erdometo/fluxgate-project/Pictures/1686348193057.jpg

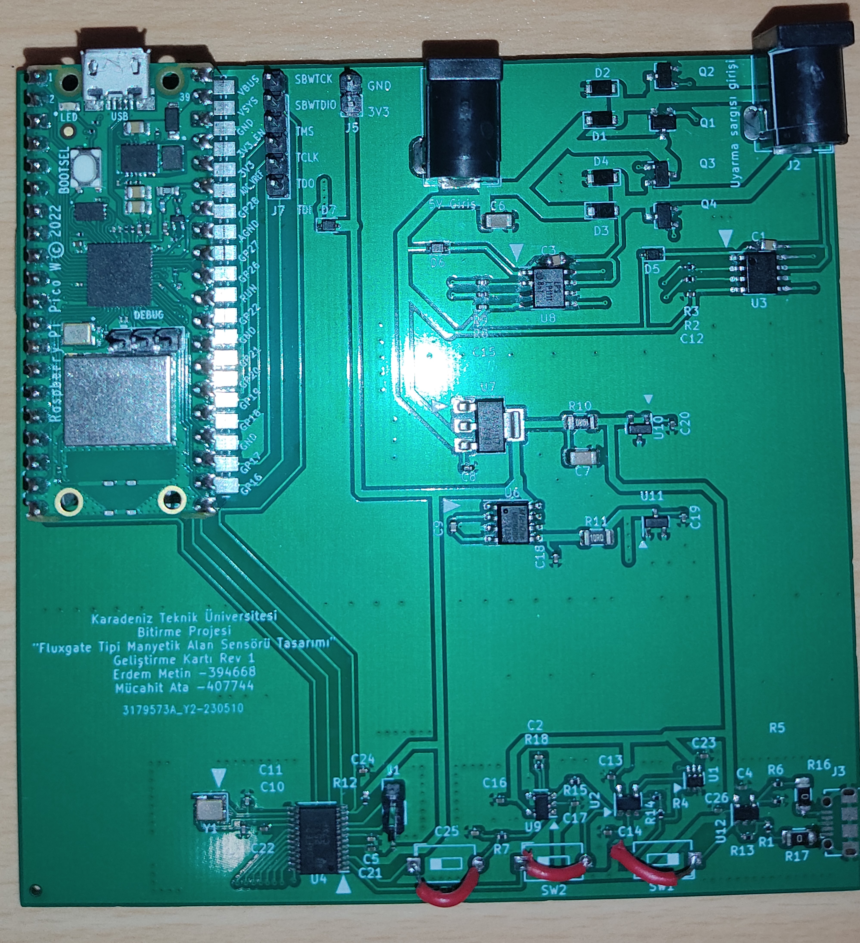
Pictures/1686348193057.jpg
