erdometo/fluxgate-project/Software/Python_GUI_Demo/ölçümler/20230616_190529.jpg

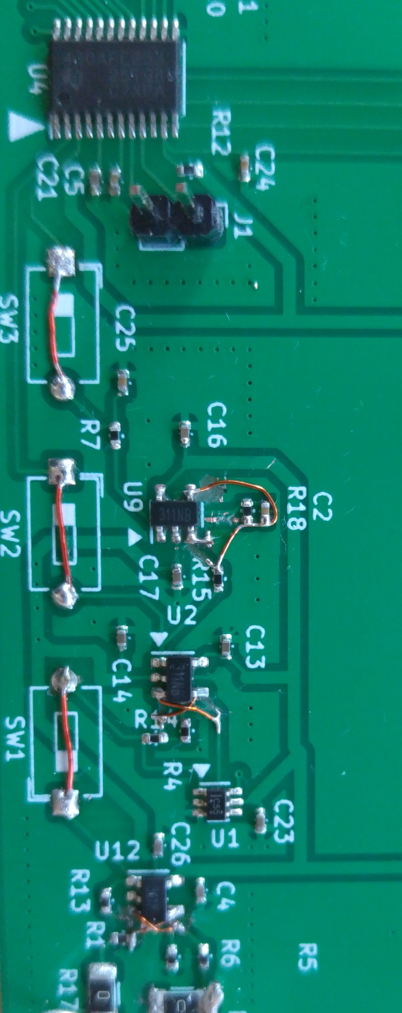
Software/Python_GUI_Demo/ölçümler/20230616_190529.jpg
