erdometo/fluxgate-project/Simulations/LTSpice/Draft1.asc

J1: njf; 2N5485
R1: res; 1K; tol=1 pwr=0.1
V1: voltage; 5
V2: voltage; 5
Named nets: 0
