erdometo/fluxgate-project/Simulations/LTSpice/Draft2.asc

C1: cap
L1: ind
R1: res
Named nets: 0, Eo, Ei
Z1
Z2
