erdometo/fluxgate-project/Simulations/LTSpice/Draft3.asc

C1: cap; 2m
C2: cap; 500µ
L1: ind; 200m
R1: res; 5m
R2: res; 12.5k
R3: res; 10
R4: res; 1
R5: res; 60
R6: res; 1k
R7: res; 1k
R8: res; 1k
R9: res; 1k
U1: opamp
U2: opamp
U3: opamp
V1: voltage; PULSE(0 50 0 0 0 0.5m 1m 100000)
V2: voltage; 5
Named nets: 0
.tran 2 steady startup
