erdometo/fluxgate-project/Simulations/LTSpice/Draft4.asc

L1: ind2; 500n
L2: FerriteBead; 1000n; Ipk=0.2 Rser=0.562 Rpar=750 Cpar=350f
L3: FerriteBead; 1000n; Ipk=0.2 Rser=0.562 Rpar=750 Cpar=350f
R1: res; 2
R2: res; 1T
R3: res; 2
V1: voltage; PULSE(-2 2 0 0.1p 0.1p 2u 4u)
V2: voltage; SINE(0 2 1000000)
V3: voltage; 1
Named nets: Vo, 0, VO2
.tran 0 0.00005 0 startup
K1 L3  L2  1
