erdometo/fluxgate-project/Simulations/LTSpice/Draft5.asc

D1: diode
D2: diode
D3: diode
D4: diode
L1: ind2; 1.3m
L2: ind2; 1.3m
M1: nmos; IRFZ44N
M2: nmos; IRFZ44N
M3: nmos; IRFZ44N
M4: nmos; IRFZ44N
R1: res; 3
V1: voltage; 12
V2: voltage; PULSE(0 20 0 0 0 0.0001 0.0004)
V3: voltage; PULSE(0 20 0.0002 0 0 0.0001 0.0004)
Named nets: 0, +vo, -vo
.tran 0 0.01 0
K L1 L2 1
