erdometo/fluxgate-project/Simulations/LTSpice/Draft6.asc

100u: cap; 100µ
M1: nmos; IRFZ44N
Q1: npn; BC547B
Q2: npn; BC547B
Q4: npn; 2SD2652
Q5: npn3; 2SCR375P
R1: res; 2
R2: res; 1000
R3: res; 10; tol=1 pwr=0.1
R4: res; 10000
R5: res; 1000
R6: res; 2
V1: voltage; 5
V2: signal; PULSE(0 3.5 0 0 0 2500u 5800u)
Named nets: 0
.tran 0 1.1 1 00.1
