erdometo/fluxgate-project/Simulations/LTSpice/driver.asc

C1: cap; 1µ
C2: cap; 10µ
C3: cap; 1µ
C4: cap; 10µ
D1: diode
D2: diode
D3: diode
D4: diode
D5: diode; 1N4148
D6: diode; 1N4148
L1: ind2; 1.3m
L2: ind2; 1.2m
L3: ind2; 0.003m
M1: nmos; IRFZ44N
M2: nmos; IRFZ44N
M3: nmos; IRFZ44N
M4: nmos; IRFZ44N
R1: res; 3
U1: LT1162
U2: LT1162
V1: voltage; 12
V2: voltage; PULSE(0 20 0 0 0 0.0001 0.0004)
V3: voltage; PULSE(0 20 0.0002 0 0 0.0001 0.0004)
V4: voltage; 12
V5: voltage; 12
Named nets: 0, +vo, -vo, A1, A2, B1, B2, +sig
.tran 0 0.01 0
K L1 L2 L3 1
